haricane8133/parrot90/hardware/circuit/Hi res pcb.png

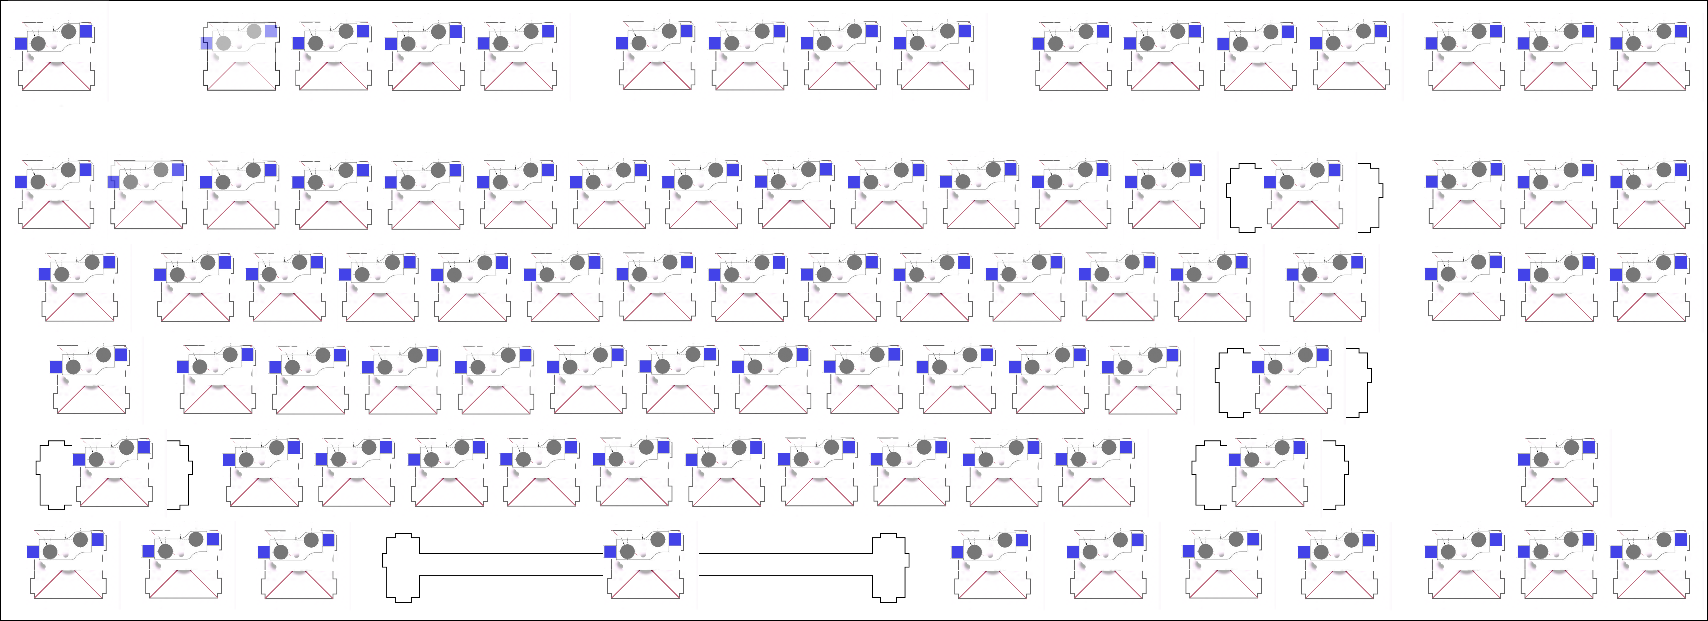
hardware/circuit/Hi res pcb.png
