haricane8133/parrot90/hardware/circuit/left_switch_layer.png

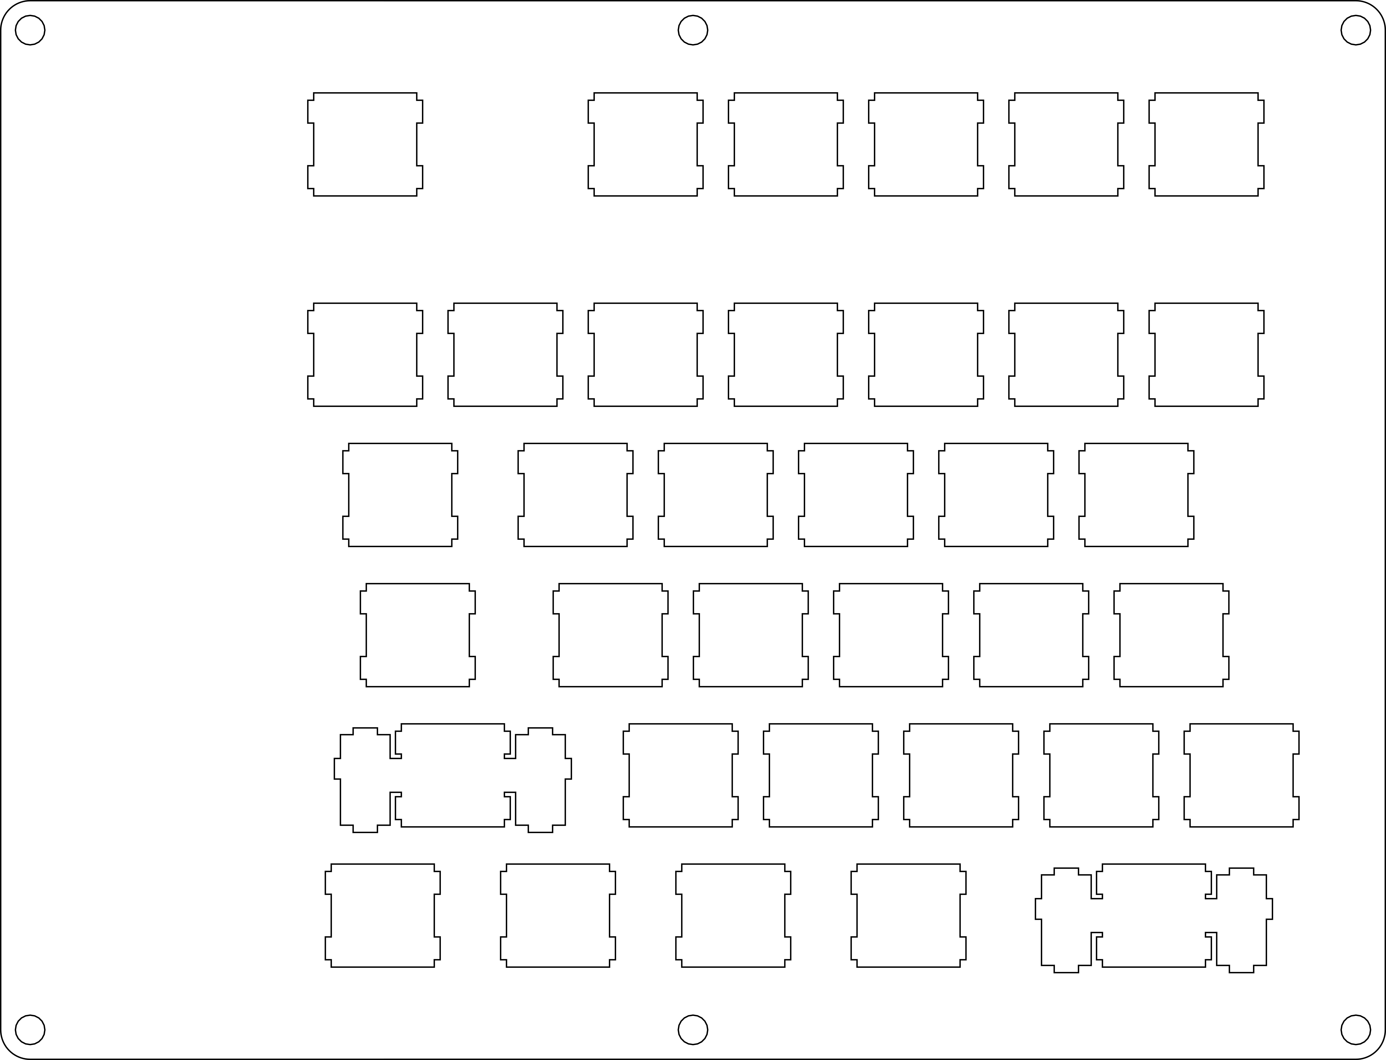
hardware/circuit/left_switch_layer.png
