haricane8133/parrot90/hardware/circuit/left_switch_layer_pcb_1.png

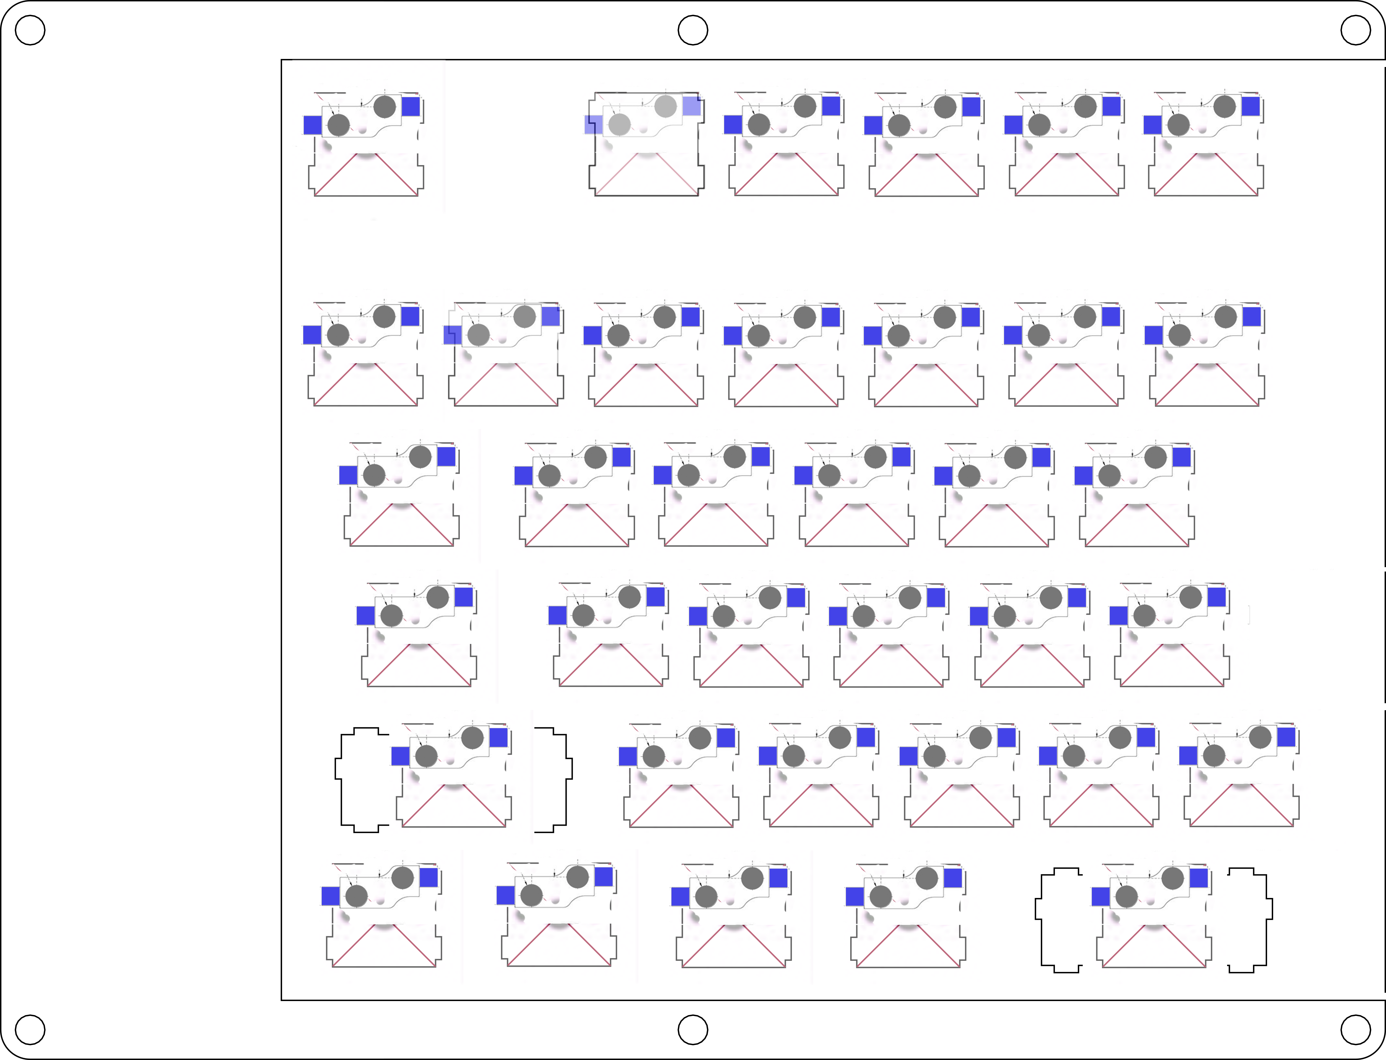
hardware/circuit/left_switch_layer_pcb_1.png
