haricane8133/parrot90/hardware/circuit/left_switch_layer_pcb_2.png

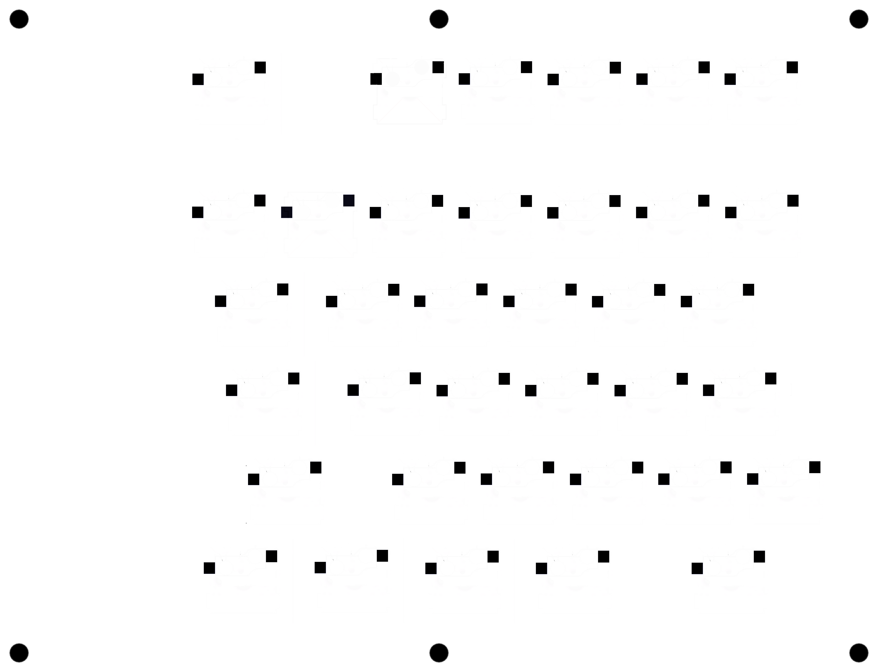
hardware/circuit/left_switch_layer_pcb_2.png
