haricane8133/parrot90/hardware/circuit/left_switch_layer_pcb_3_top.png

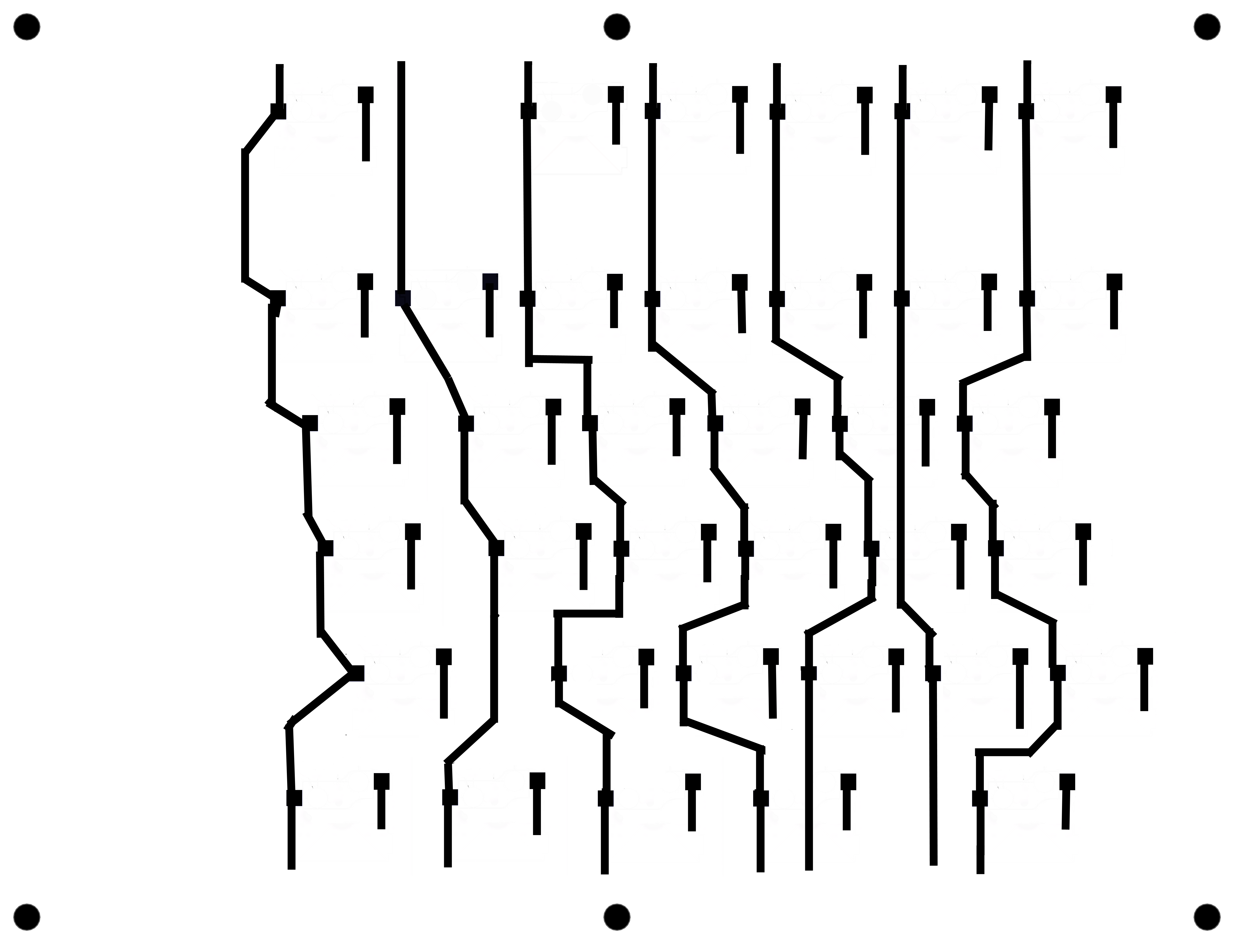
hardware/circuit/left_switch_layer_pcb_3_top.png
