haricane8133/parrot90/hardware/circuit/left_switch_layer_pcb_4_top.png

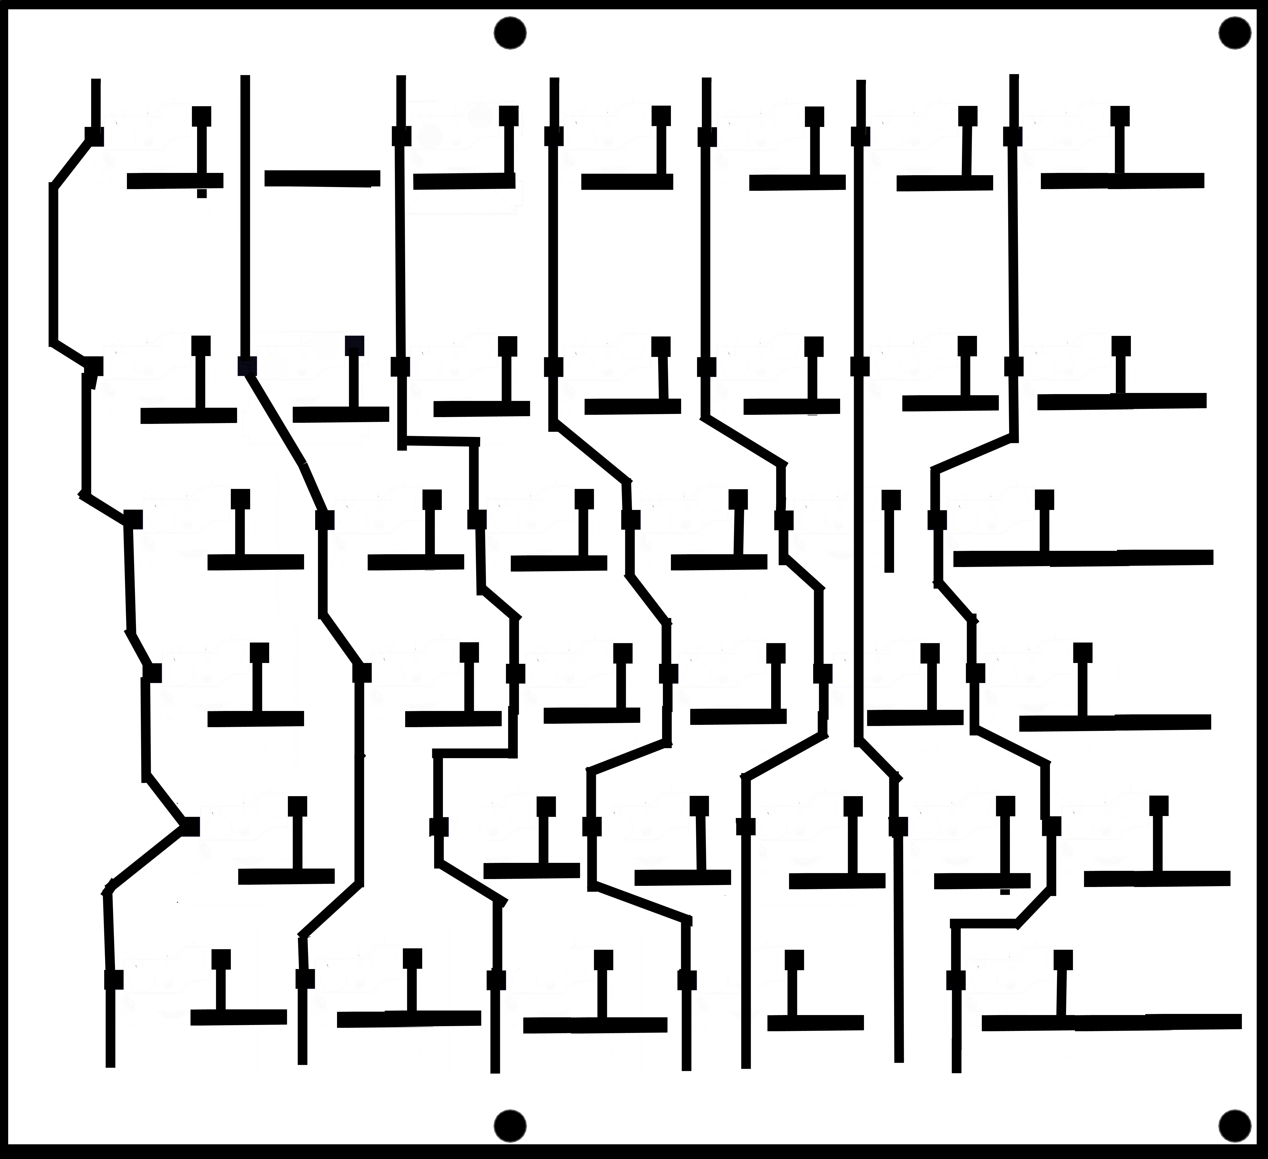
hardware/circuit/left_switch_layer_pcb_4_top.png
