haricane8133/parrot90/hardware/circuit/pico.jpg

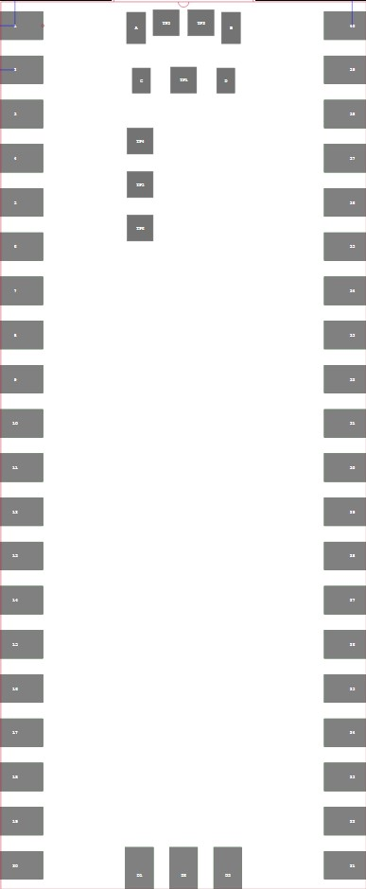
hardware/circuit/pico.jpg
