haricane8133/parrot90/hardware/circuit/pico.png

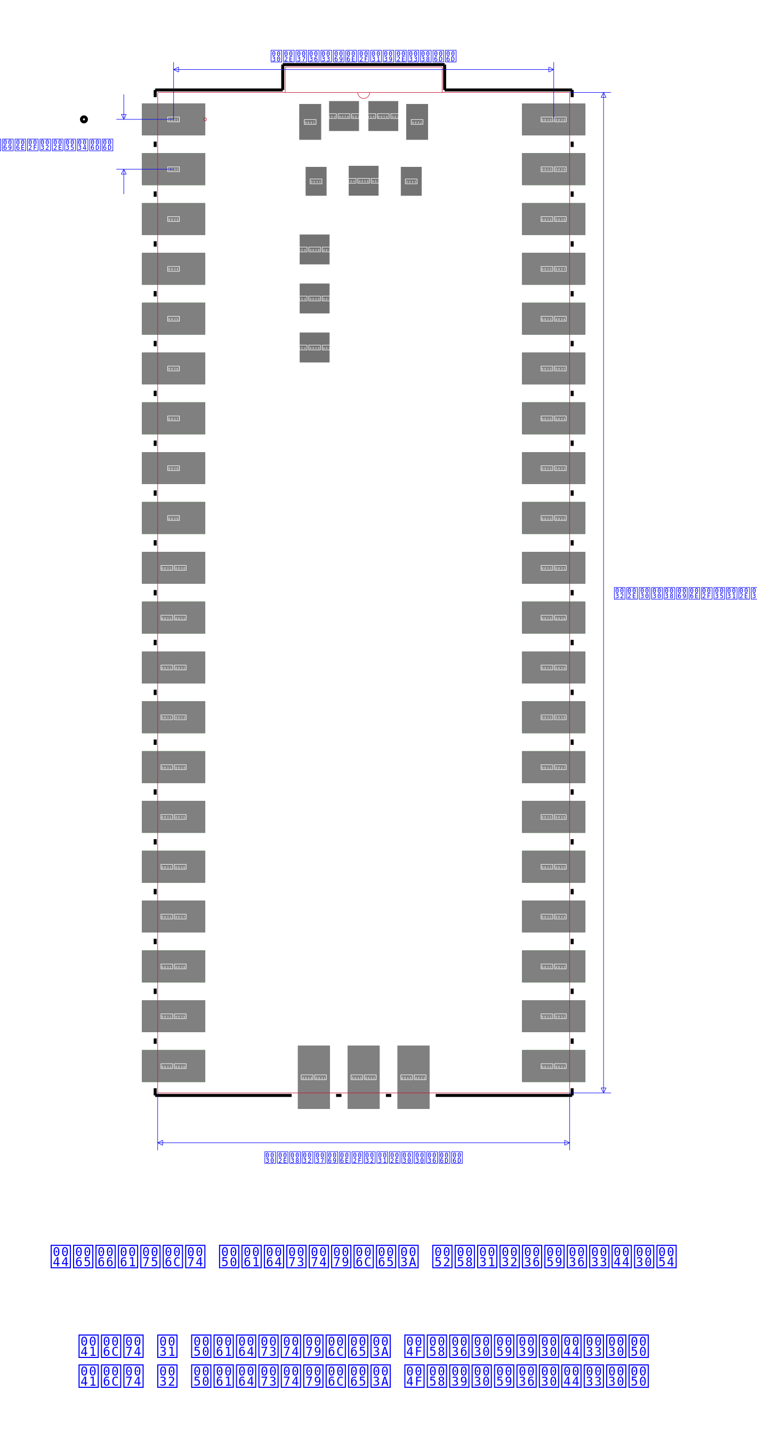
hardware/circuit/pico.png
