haricane8133/parrot90/hardware/circuit/right_switch_layer.png

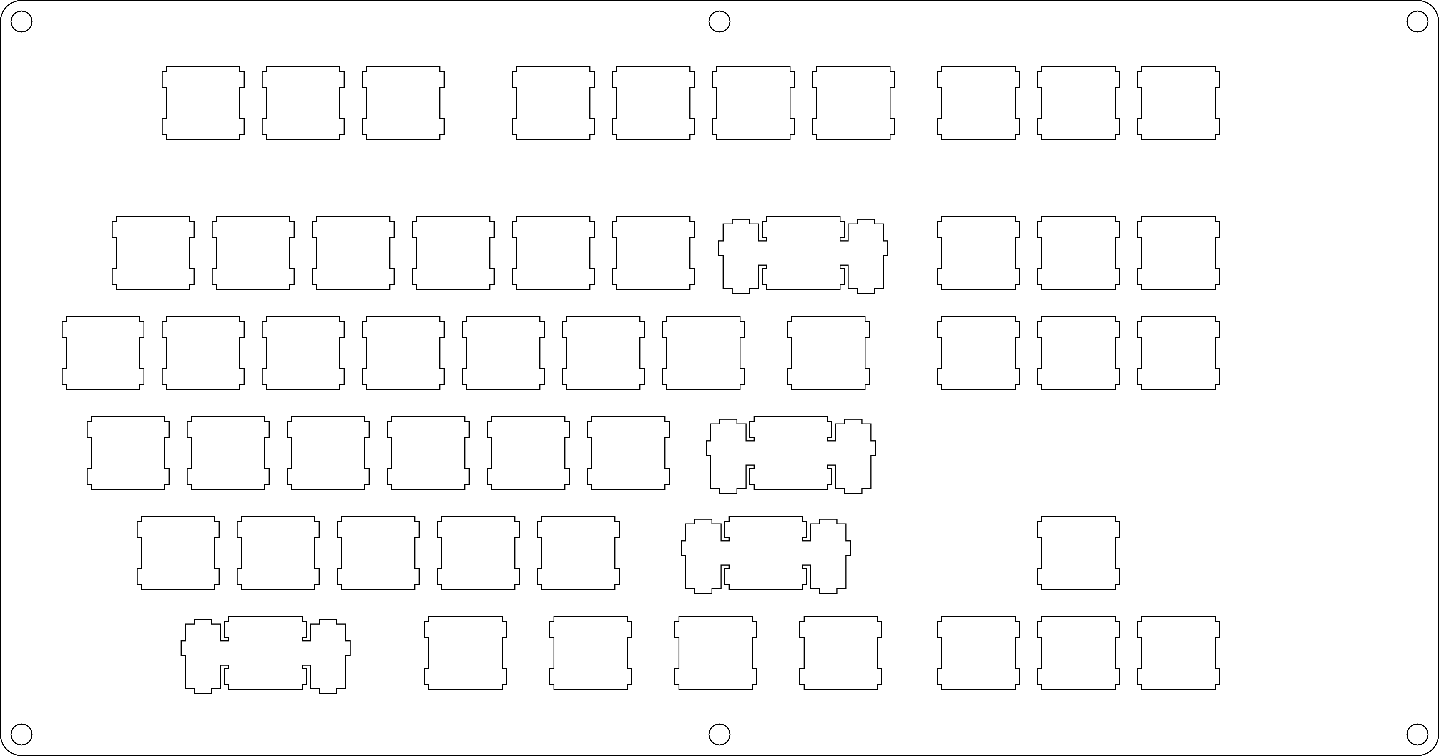
hardware/circuit/right_switch_layer.png
