haricane8133/parrot90/hardware/circuit/right_switch_layer_pcb_2.png

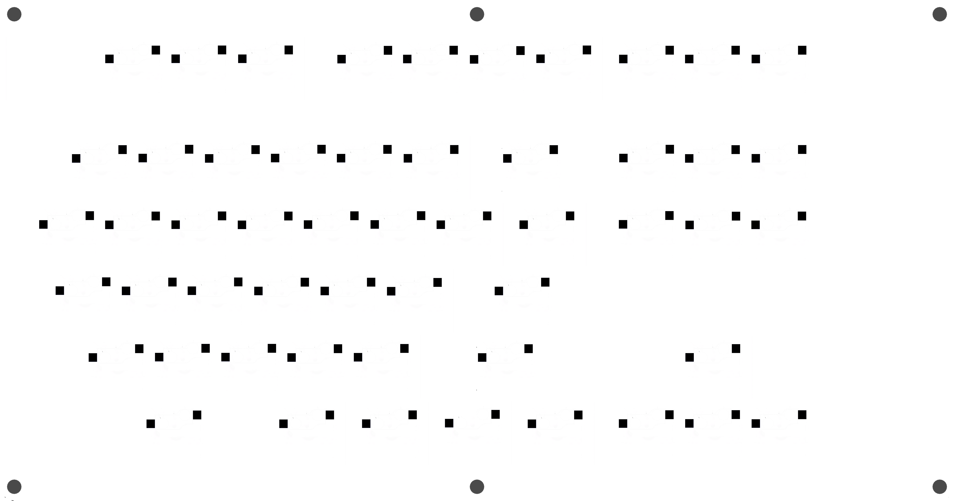
hardware/circuit/right_switch_layer_pcb_2.png
