haricane8133/parrot90/hardware/circuit/right_switch_layer_pcb_4_top.png

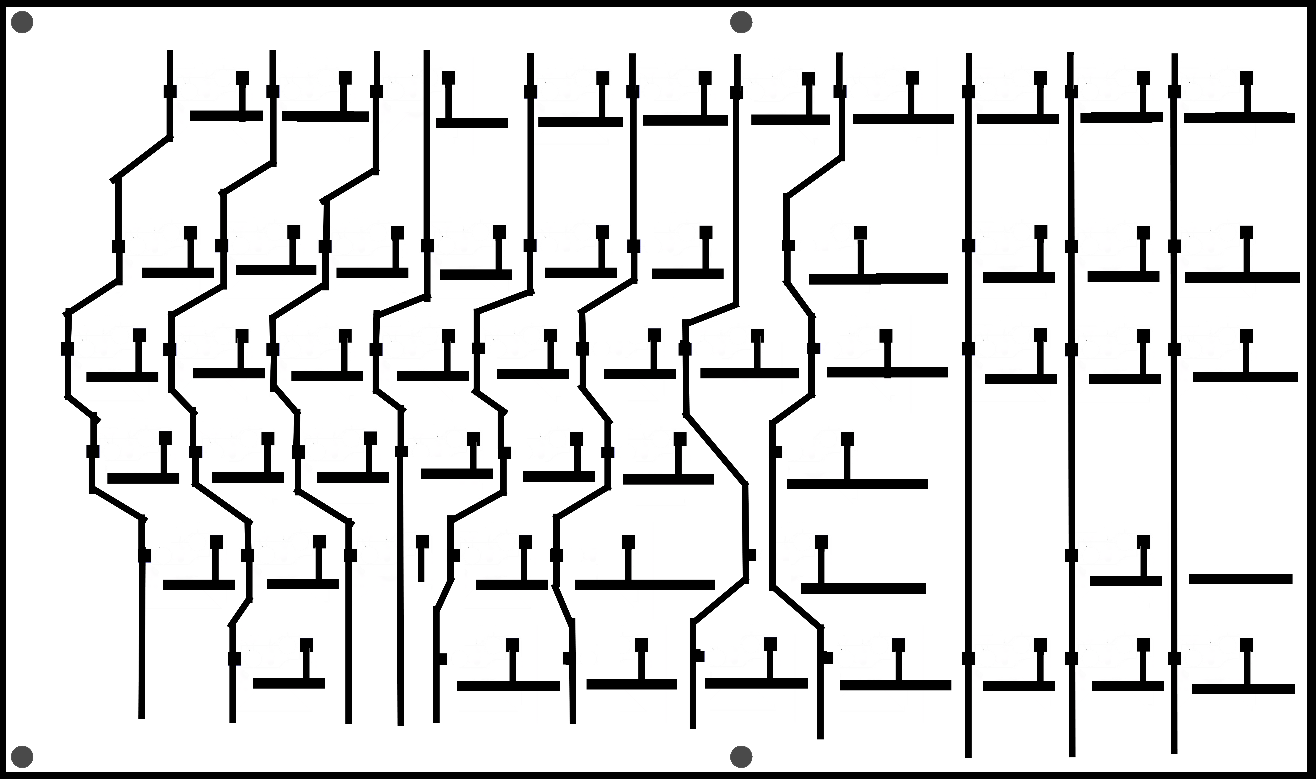
hardware/circuit/right_switch_layer_pcb_4_top.png
