haricane8133/parrot90/hardware/images/3.png

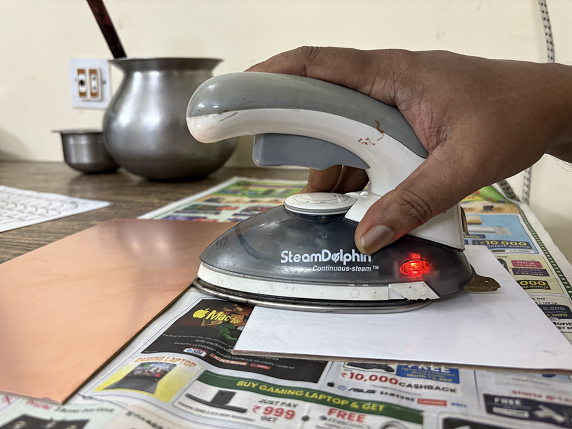
hardware/images/3.png
