haricane8133/parrot90/hardware/images/15.png

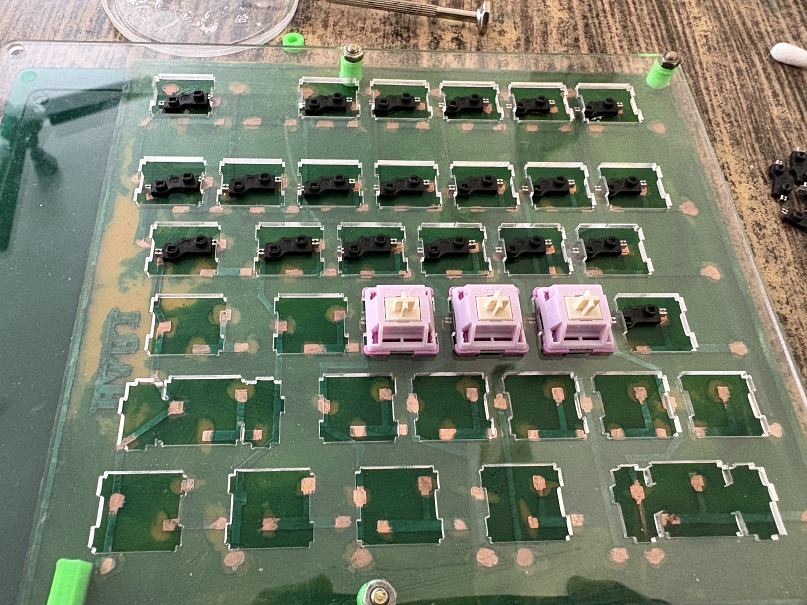
hardware/images/15.png
