haricane8133/parrot90/hardware/plate/left_layout.jpg

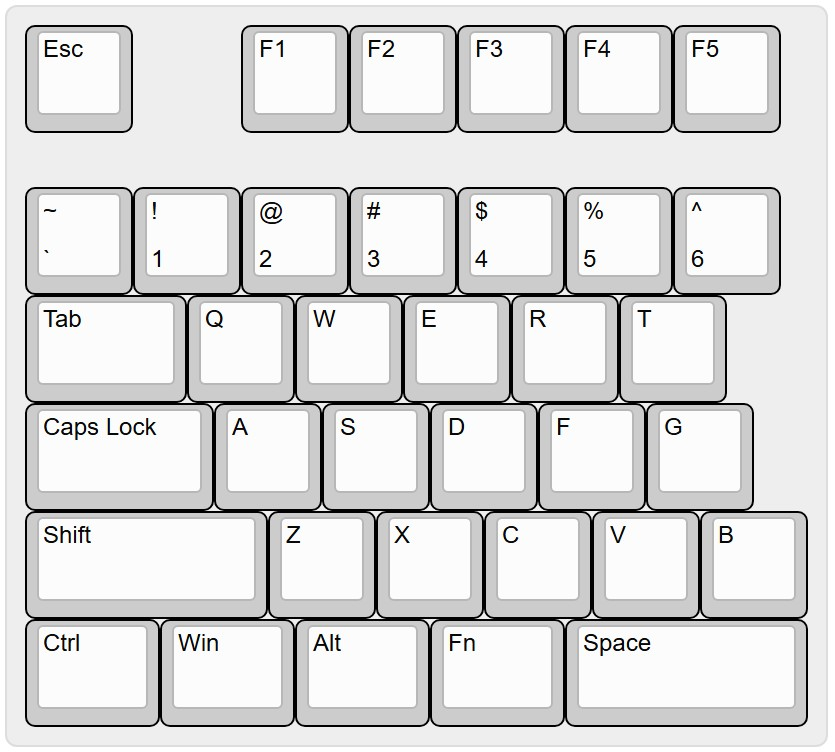
hardware/plate/left_layout.jpg
