haricane8133/parrot90/hardware/plate/right_layout.jpg

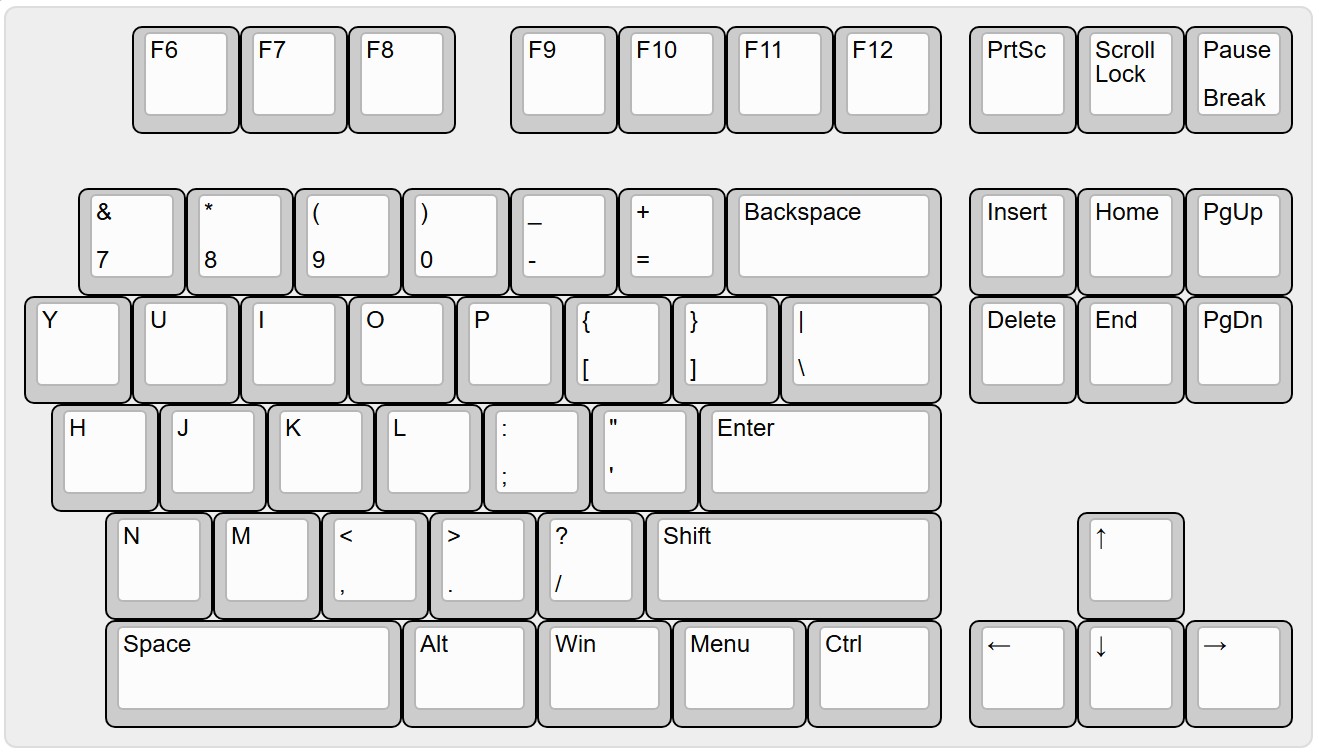
hardware/plate/right_layout.jpg
